BusyPear/XLR8-RoboRenegade/Bot circuit.jpg

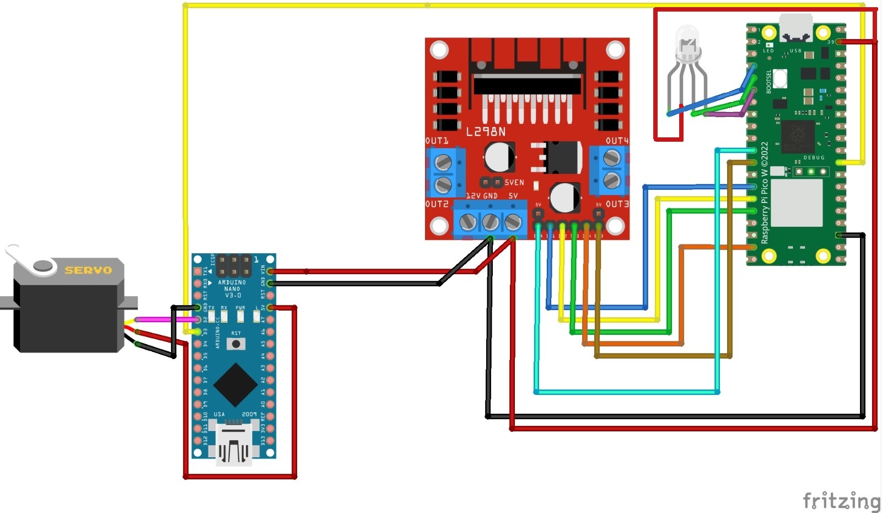
Bot circuit.jpg
