BusyPear/XLR8-RoboRenegade/RR car front view.jpg

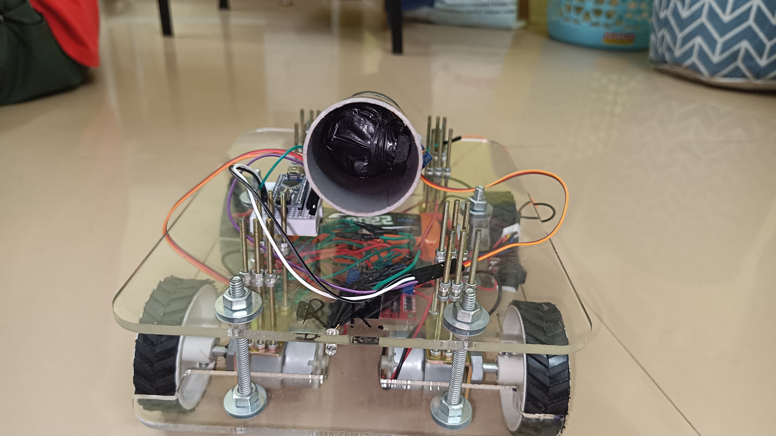
RR car front view.jpg
